Echoras/ScrapPi/images/CaseUnboxed3.jpeg

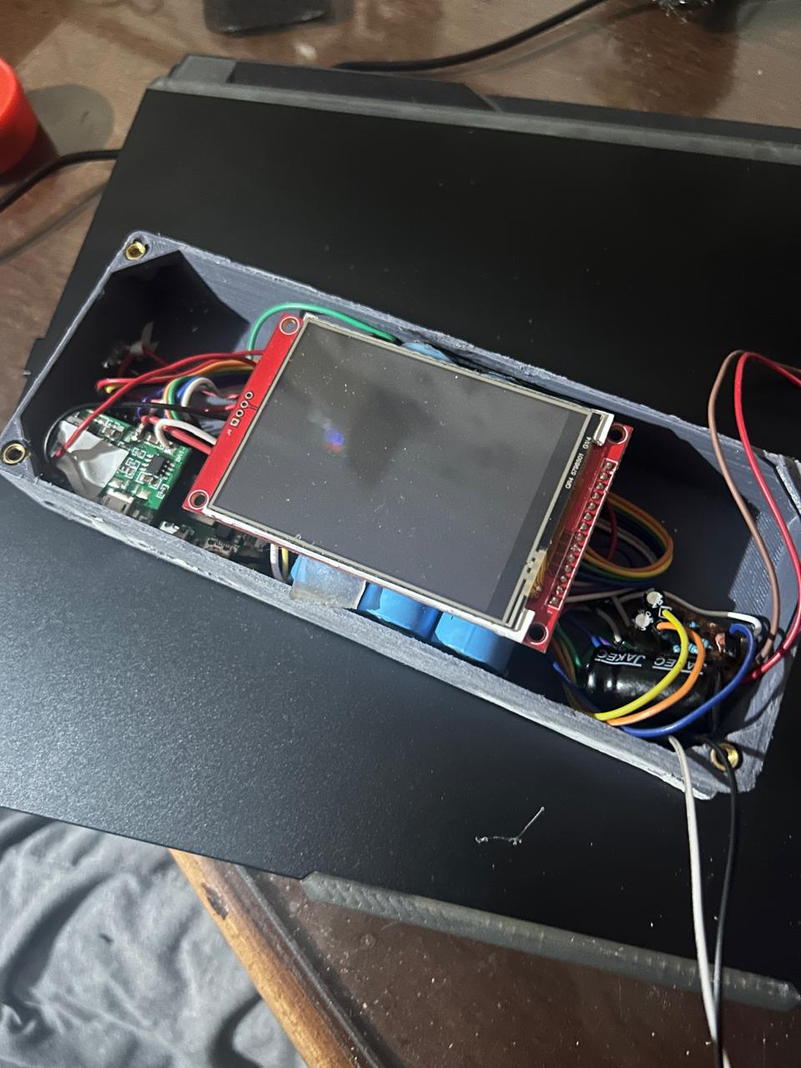
images/CaseUnboxed3.jpeg
