Echoras/ScrapPi/images/Pirunnin.jpeg

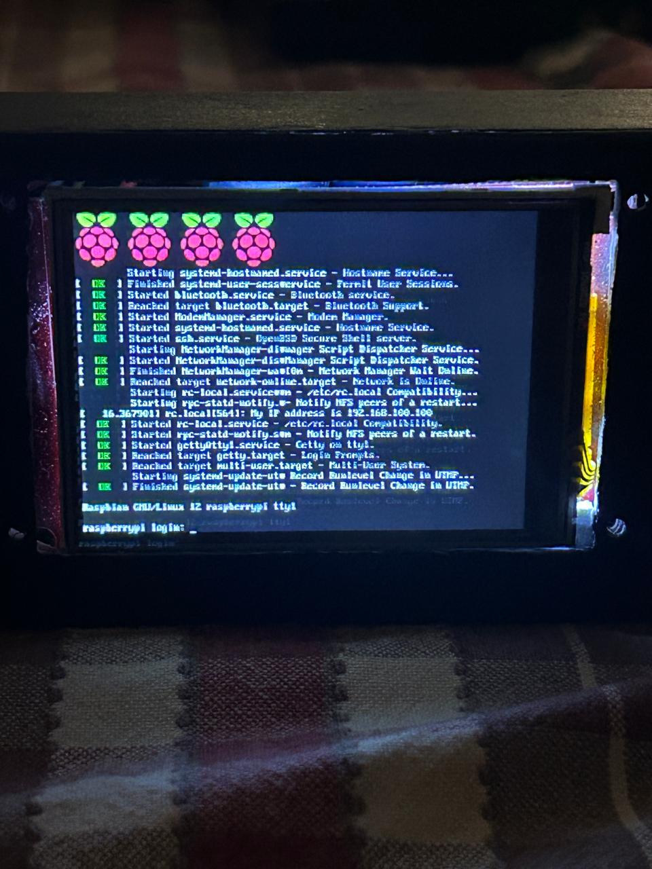
images/Pirunnin.jpeg
